HadleyResearch/RGBSaber/Firmware/v2.0/C/constants.h

/*
 * File: constants.h
 * Author: George Hadley
 * Description: constants used in the RGBSaber Firmware v2.0
 */

 //Memory storage locations for red/green/blue pwm values
 #define REDMEM 	0
 #define GREENMEM	1
 #define BLUEMEM	2

 //Timing Constants (interrupt counts
 #define SECOND		122
 #define MINUTE		60
 #define EXPIRE		1

 //Other Definitions
 #define FLASHVAL	32
